modernhousetech/waterwatch/delme/IMG_1665 (1).jpeg

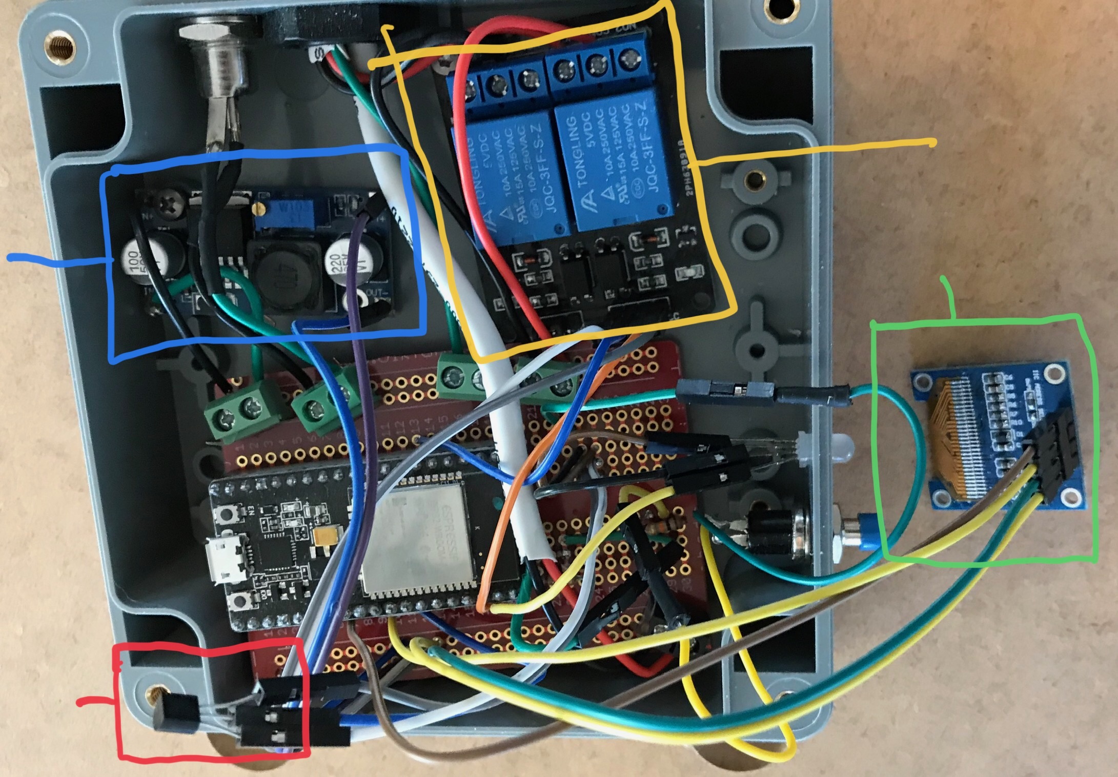
delme/IMG_1665 (1).jpeg
