modernhousetech/waterwatch/delme/IMG_1665.jpeg

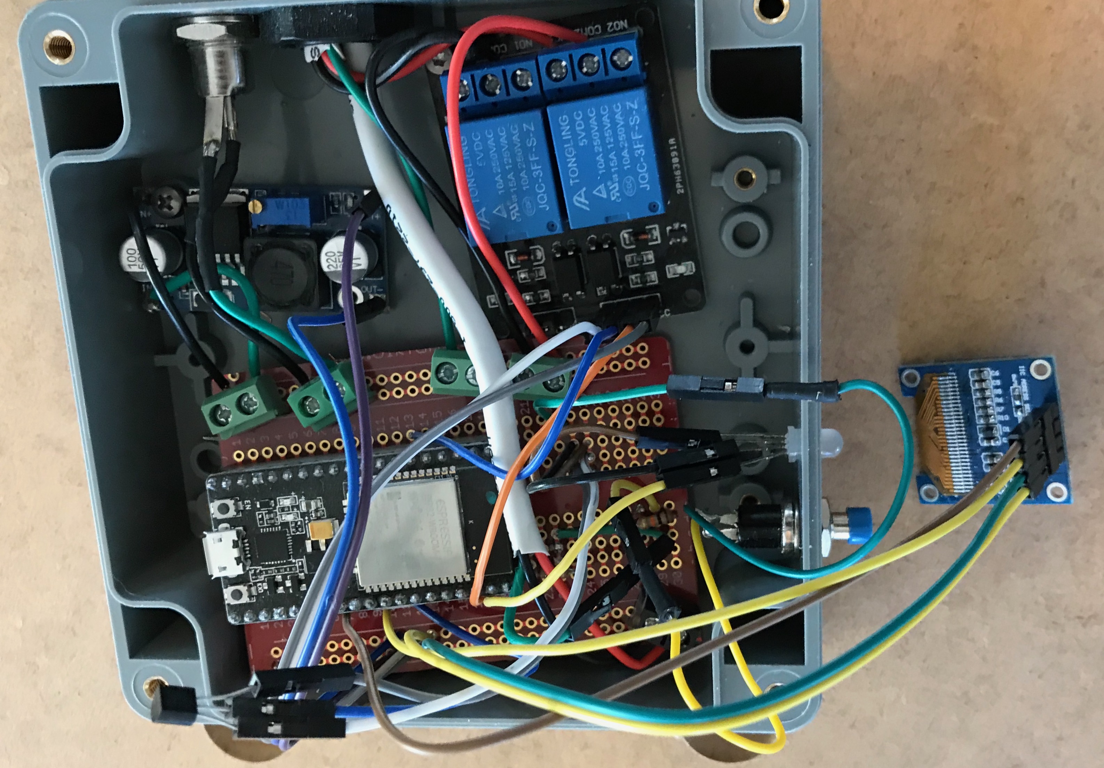
delme/IMG_1665.jpeg
