modernhousetech/waterwatch/delme/wwh_dev1.jpeg

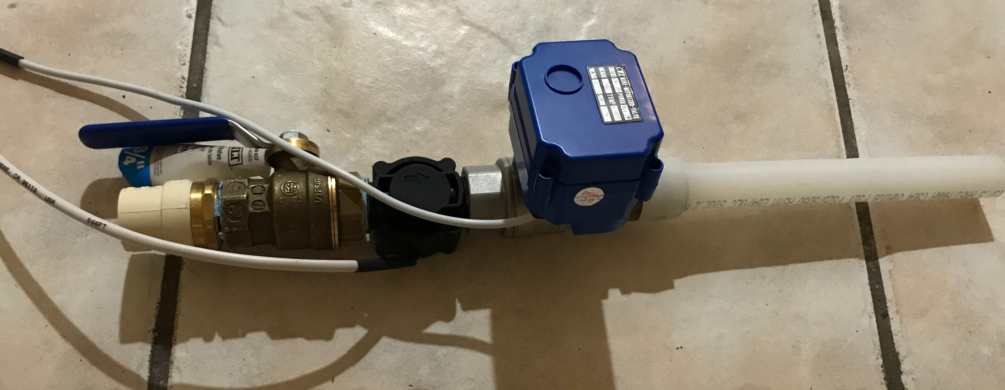
delme/wwh_dev1.jpeg
