modernhousetech/waterwatch/water_flow_sensor.cpp

#include "water_flow_sensor.h"


// char const *string22 = R"someToken({
//   "name": "software rendering list",
//   "version": "10.9",
//   "entries": [
//     {
//       "id": 1,
//       "description": "ATI Radeon X1900 is not compatible with WebGL on the Mac",
//       "webkit_bugs": [47028],
//       "os": {
//         "type": "macosx"
//       },
//       "vendor_id": "0x1002",
//       "device_id": ["0x7249"],
//       "features": [
//         "webgl",
//         "flash_3d",
//         "flash_stage3d"
//       ]
//     },
//     {
//       "id": 3,
//       "description": "GL driver is software rendered. GPU acceleration is disabled",
//       "cr_bugs": [59302, 315217],
//       "os": {
//         "type": "linux"
//       },
//       "gl_renderer": "(?i).*software.*",
//       "features": [
//         "all"
//       ]
//     }
//   ]
// })someToken";
